flamefir/Macro-Pro/information/prototype_design_build/5392361781820198669.png

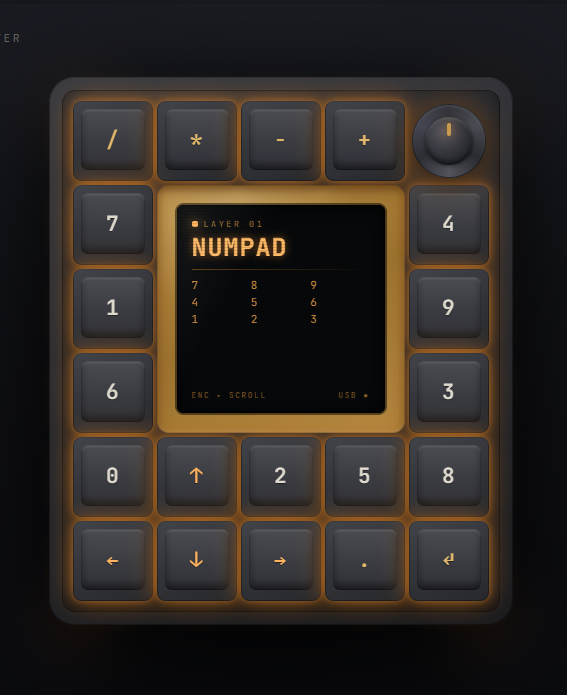
information/prototype_design_build/5392361781820198669.png
