flamefir/Macro-Pro/information/prototype_design_build/context_pcb_b.png

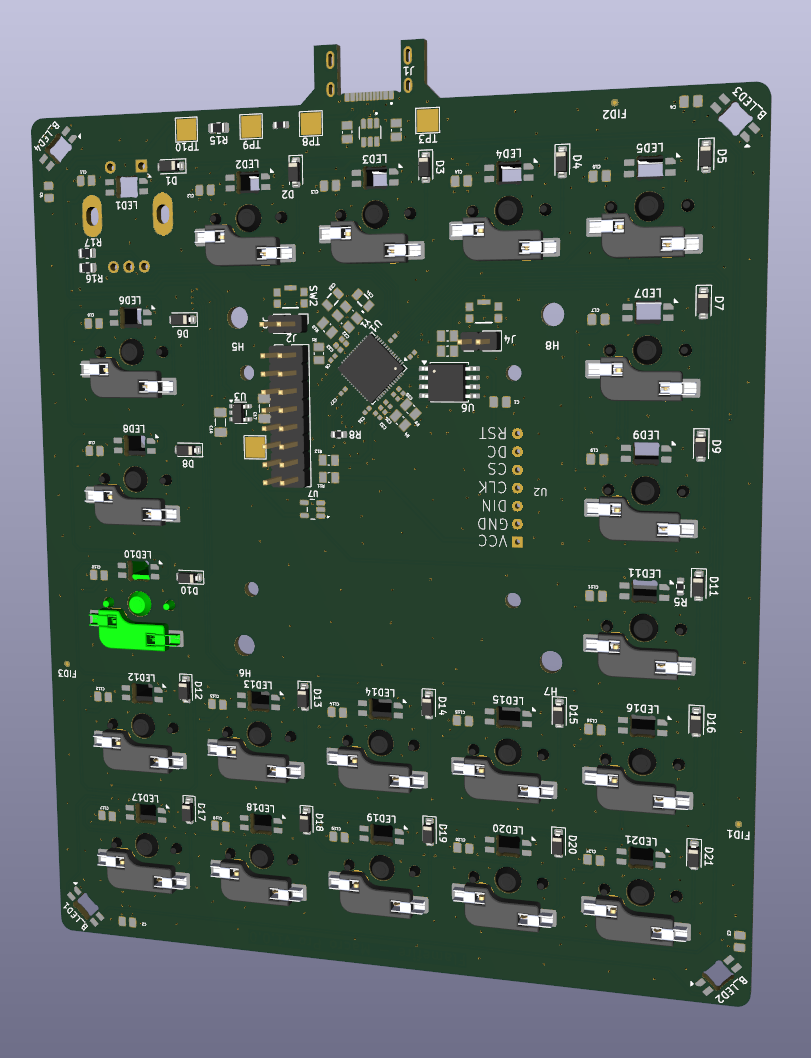
information/prototype_design_build/context_pcb_b.png
